kianfrassekkk/EEE4120F_nest_temperature_control/kian/kian nest microcontroler ESP32/microcontroler.kicad_sch

## KiCad design kian/kian nest microcontroler ESP32/microcontroler.kicad_sch (2024-05-17)

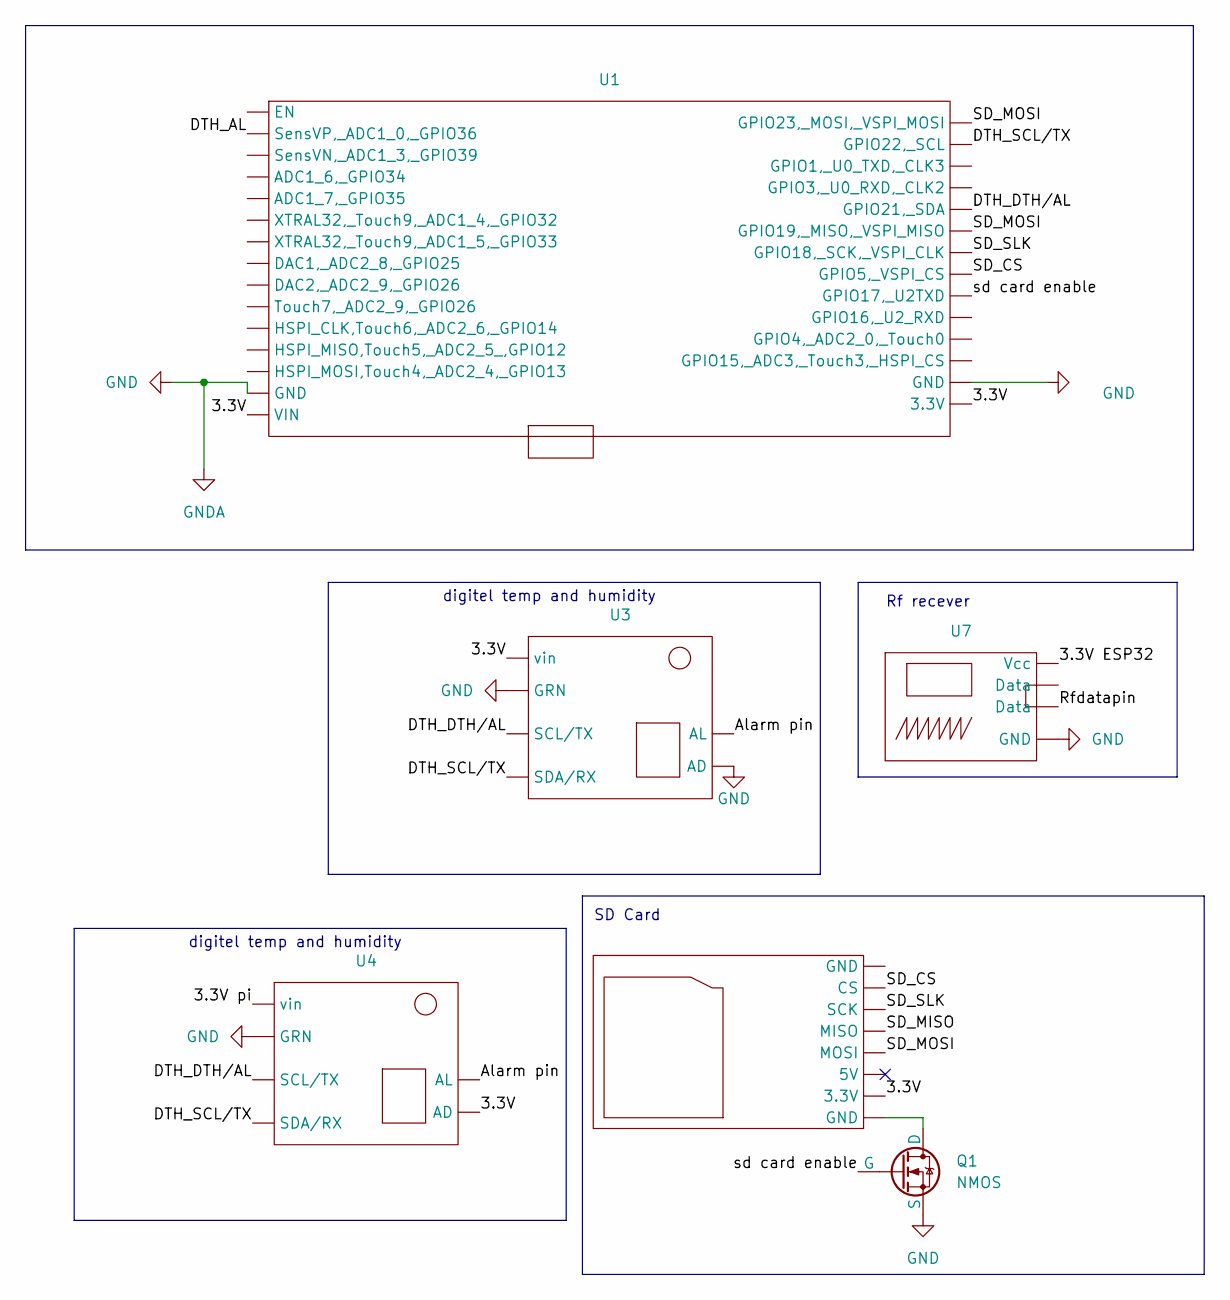
[picture p2: schematic microcontroler.kicad_sch]

Parts:
Q1: NMOS
U1, U3, U4, U7: (no value)
e: (no value)

Connections:
3.3V: U1., U3., U4., e.
3.3V ESP32: U7.
3.3V pi: U4.
Alarm pin: U3., U4.
DTH_AL: U1.
DTH_DTH/AL: U1., U3., U4.
DTH_SCL/TX: U1., U3., U4.
GND: Q1.3 (S), U1., U3., U4., U7.
unnamed: Q1.1 (D), e.
Rfdatapin: U7.
SD_CS: U1., e.
SD_MISO: e.
SD_MOSI: U1., e.
SD_SLK: U1., e.
sd card enable: Q1.2 (G), U1.

Notes on the sheet:
Rf recever
digitel temp and humidity
SD Card
