kianfrassekkk/EEE4120F_nest_temperature_control/kian/kian recever microcontroler subsection ESP32/microcontroler.kicad_sch

## KiCad design kian/kian recever microcontroler subsection ESP32/microcontroler.kicad_sch (2024-05-17)

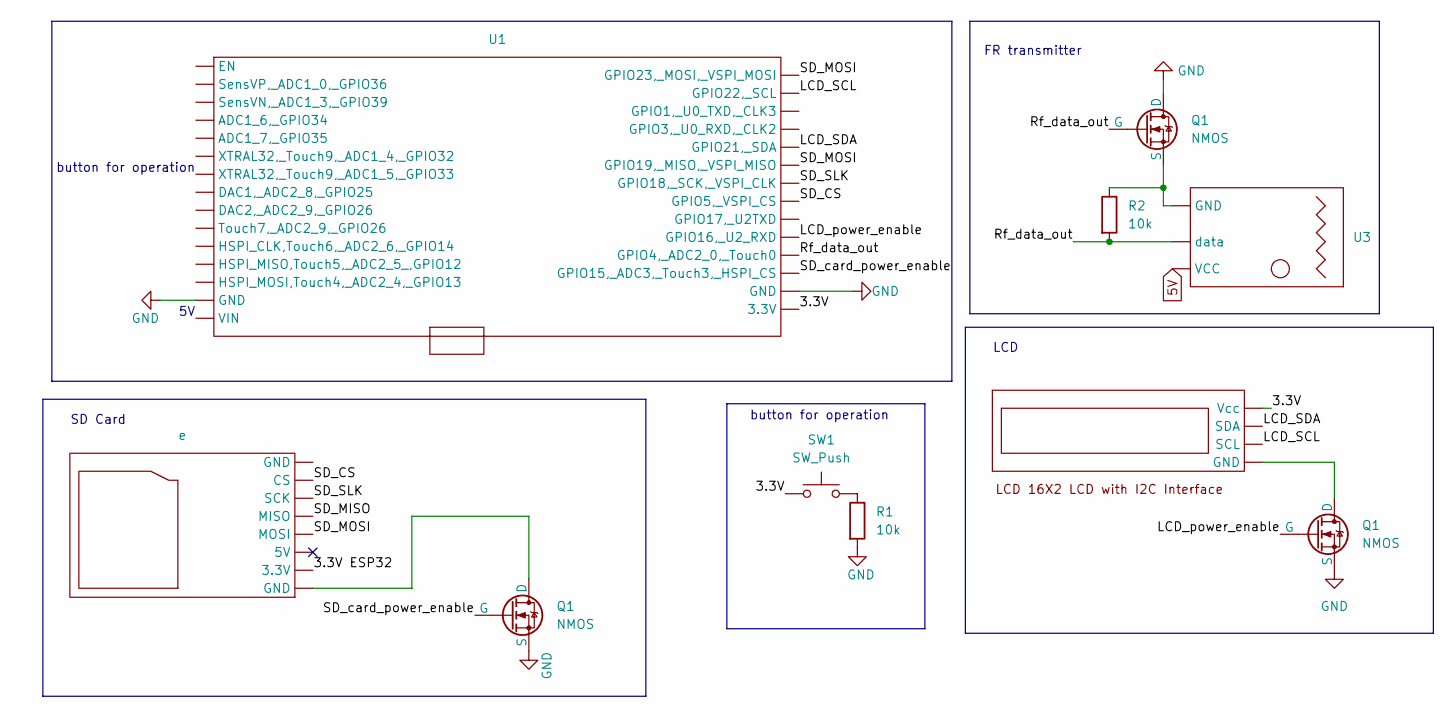
[picture p3: schematic microcontroler.kicad_sch]

Parts:
Q1: NMOS
R1, R2: 10k
SW1: SW_Push
U1, U3: (no value)
e: (no value)

Connections:
3.3V: SW1.1, U1.
3.3V ESP32: e.
5V: U3.
GND: Q1.1 (D), Q1.3 (S), R1.2, U1.
LCD_SCL: U1.
LCD_SDA: U1.
LCD_power_enable: Q1.2 (G), U1.
unnamed: Q1.1 (D), U1., e.
unnamed: Q1.3 (S), R2.1, U3.
unnamed: R1.1, SW1.2
Rf_data_out: Q1.2 (G), R2.2, U1., U3.
SD_CS: U1., e.
SD_MISO: e.
SD_MOSI: U1., e.
SD_SLK: U1., e.
SD_card_power_enable: Q1.2 (G), U1.

Notes on the sheet:
FR transmitter
SD Card
button for operation
LCD
